Elecrow-RD/CrowPanel--ESP32-Display-1.28-R-inch-240240/example/micropython/MicroPython-1.28-Demo/examples/LCD.py

from machine import Pin,I2C
from pi4ioe5v6408ztaex import PI4IOE5V6408
from gc9a01 import LCD_1inch28 
import time
        
# Initialize the I2C bus with the specified pins and frequency
i2c = I2C(0, sda=Pin(4), scl=Pin(5), freq=400_000)

# Create an instance of the PI4IOE5V6408 class with the I2C bus
io_expander = PI4IOE5V6408(i2c)

io_expander.write_pin(4, True)
time.sleep(1)
io_expander.write_pin(2, True)
time.sleep(1)

LCD = LCD_1inch28()
LCD.text("Elecrow",90,120,LCD.blue)
LCD.show()
time.sleep(5)
    
while True:
    LCD.fill(LCD.red)
    LCD.show()
    time.sleep(1)
    LCD.fill(LCD.green)
    LCD.show()
    time.sleep(1)
    LCD.fill(LCD.blue)
    LCD.show()
    time.sleep(1)
