Elecrow-RD/CrowPanel--ESP32-Display-1.28-R-inch-240240/factory_soucecode/factory_demo/Esp32_Watch_Demo/do_mian.h

#include "Arduino.h"
#include "lvgl.h"
#include "ui.h"

//set up the touch screen
#define is_touch 1
//set up the auto play
#define is_auto_play 1
//set up the now_auto play
extern int now_is_auto_play;

void ui_mian(void);
//void auto_play(void);
